Piscitelli98/Progetto-Maturit-/Materiale/Protocolli/Diagrammi Sequenza/Immagini/Protocollo_GetAccessi.png

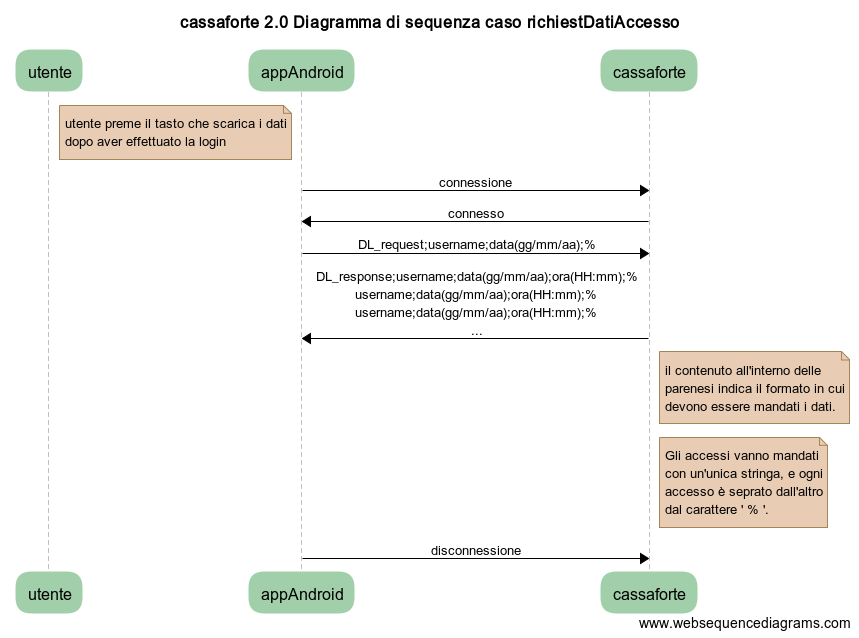
Materiale/Protocolli/Diagrammi Sequenza/Immagini/Protocollo_GetAccessi.png
