Piscitelli98/Progetto-Maturit-/Materiale/Schemi/Circuito completo.png

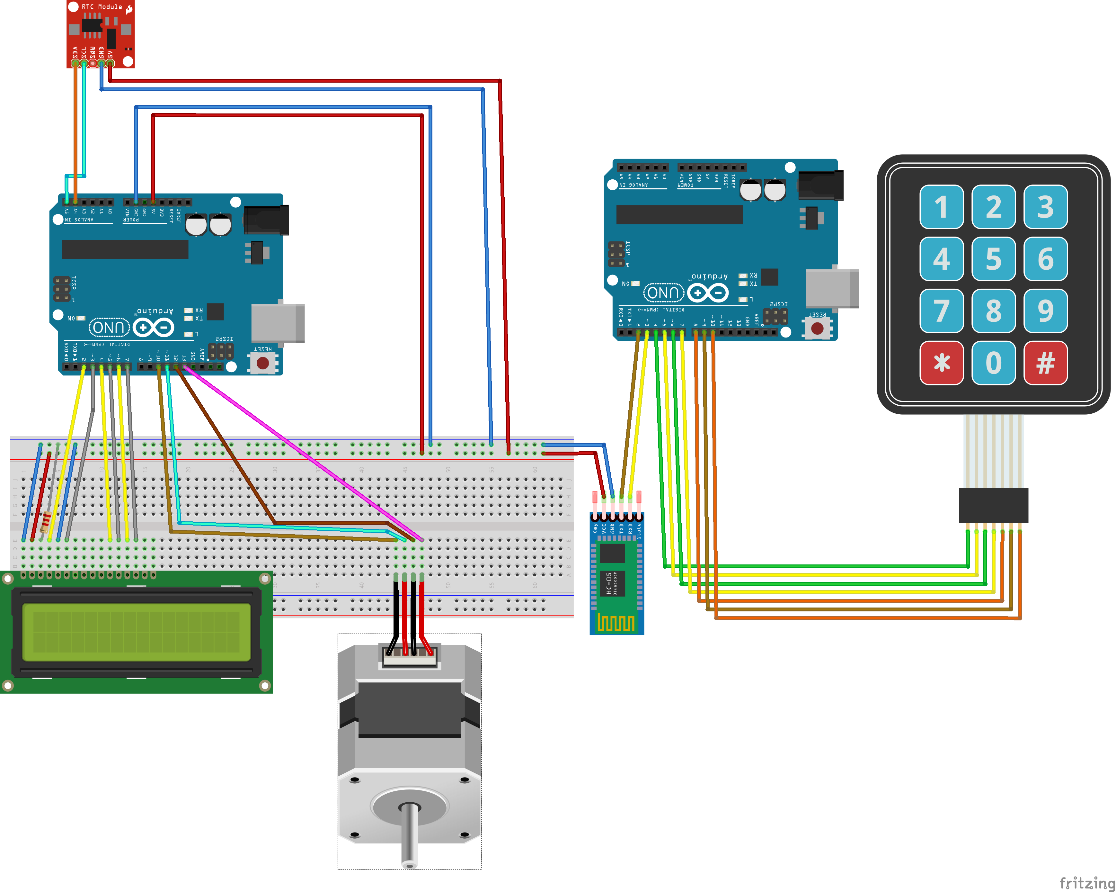
Materiale/Schemi/Circuito completo.png
