Piscitelli98/Progetto-Maturit-/Materiale/Schemi/RTC DS3232.png

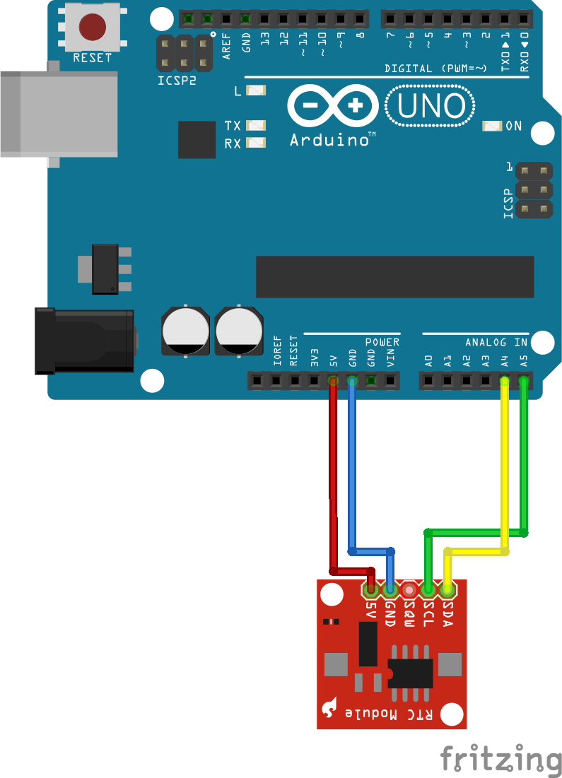
Materiale/Schemi/RTC DS3232.png
