Piscitelli98/Progetto-Maturit-/Materiale/Arduino/arduinoCam.ino

// ArduCAM demo (C)2014 Lee
// web: http://www.ArduCAM.com
// This program is a demo of how to use most of the functions
// of the library with a supported camera modules.
//
// This demo was made for Omnivision OV7670 sensor.
// It will turn the ArduCAM into a real digital camera with capture and playback functions.
// 1. Preview the live video on LCD Screen.
// 2. Capture and buffer the image to FIFO when shutter pressed quickly.
// 3. Store the image to Micro SD/TF card with BMP format.
// 4. Playback the capture photos one by one when shutter buttom hold on for 3 seconds.
// This program requires the ArduCAM V3.1.0 (or above) library and Rev.C ArduCAM shield
// and use Arduino IDE 1.5.2 compiler or above

#include <UTFT_SPI.h>
#include <SD.h>
#include <Wire.h>
#include <ArduCAM.h>
#include <SPI.h>
#include "memorysaver.h"

#if defined(__arm__)
  #include <itoa.h>
#endif

#define SD_CS 9 
#define BMPIMAGEOFFSET 66

// set pin 10 as the slave select for the ArduCAM shield
const int SPI_CS = 10;

const char bmp_header[BMPIMAGEOFFSET] PROGMEM =
{
      0x42, 0x4D, 0x36, 0x58, 0x02, 0x00, 0x00, 0x00, 0x00, 0x00, 0x42, 0x00, 0x00, 0x00, 0x28, 0x00, 
      0x00, 0x00, 0x40, 0x01, 0x00, 0x00, 0xF0, 0x00, 0x00, 0x00, 0x01, 0x00, 0x10, 0x00, 0x03, 0x00, 
      0x00, 0x00, 0x00, 0x58, 0x02, 0x00, 0xC4, 0x0E, 0x00, 0x00, 0xC4, 0x0E, 0x00, 0x00, 0x00, 0x00, 
      0x00, 0x00, 0x00, 0x00, 0x00, 0x00, 0x00, 0xF8, 0x00, 0x00, 0xE0, 0x07, 0x00, 0x00, 0x1F, 0x00,
      0x00, 0x00
};
  


ArduCAM myCAM(OV7670,SPI_CS);
UTFT myGLCD(SPI_CS);

void setup()
{
  uint8_t vid,pid;
  uint8_t temp; 
  
  #if defined (__AVR__)
    Wire.begin(); 
  #endif
  #if defined(__arm__)
    Wire1.begin(); 
  #endif
  Serial.begin(115200);
  Serial.println("ArduCAM Start!"); 

  // set the SPI_CS as an output:
  pinMode(SPI_CS, OUTPUT);

  // initialize SPI:
  SPI.begin(); 
  //Check if the ArduCAM SPI bus is OK
  myCAM.write_reg(ARDUCHIP_TEST1, 0x55);
  temp = myCAM.read_reg(ARDUCHIP_TEST1);
  if(temp != 0x55)
  {
    Serial.println("SPI interface Error!");
    while(1);
  }
  
  //Change MCU mode
  myCAM.set_mode(MCU2LCD_MODE);
  
  //Initialize the LCD Module
  myGLCD.InitLCD();
  
  myCAM.InitCAM();
  
  //Initialize SD Card
  if (!SD.begin(SD_CS)) 
  {
    //while (1);    //If failed, stop here
    Serial.println("SD Card Error");
  }
  else
    Serial.println("SD Card detected!");
}

void loop()
{
  char str[8];
  unsigned long previous_time = 0;
  static int k = 0;
  uint8_t temp;
  myCAM.set_mode(CAM2LCD_MODE);     //Switch to CAM
  
  while(1)
  {

    if(!myCAM.get_bit(ARDUCHIP_TRIG,VSYNC_MASK))        //New Frame is coming
    {
       myCAM.set_mode(MCU2LCD_MODE);      //Switch to MCU
       myGLCD.resetXY();
       myCAM.set_mode(CAM2LCD_MODE);      //Switch to CAM
       while(!myCAM.get_bit(ARDUCHIP_TRIG,VSYNC_MASK));   //Wait for VSYNC is gone
    }
    else if(myCAM.get_bit(ARDUCHIP_TRIG,SHUTTER_MASK))
    {
       previous_time = millis();
       while(myCAM.get_bit(ARDUCHIP_TRIG,SHUTTER_MASK))
       {
         if((millis() - previous_time) > 1500)
         {
           Playback();
         }
       }
       if((millis() - previous_time) < 1500)
       {
         k = k + 1;
         itoa(k, str, 10); 
         strcat(str,".bmp");        //Generate file name
         myCAM.set_mode(MCU2LCD_MODE);      //Switch to MCU, freeze the screen 
         GrabImage(str);
       }
    }
  }
}


void GrabImage(char* str)
{
  File outFile;
  char VH,VL;
  uint8_t temp;
  byte buf[256];
  static int k = 0;
  int i,j = 0;
  
  outFile = SD.open(str,O_WRITE | O_CREAT | O_TRUNC);
  if (! outFile) 
  {
    Serial.println("Open File Error");
    return;
  }
    
  //Switch to FIFO Mode
  myCAM.write_reg(ARDUCHIP_TIM, MODE_MASK);
  //Flush the FIFO 
  myCAM.flush_fifo();    
  //Start capture
  myCAM.start_capture();
  Serial.println("Start Capture"); 

  //Polling the capture done flag
  while(!myCAM.get_bit(ARDUCHIP_TRIG,CAP_DONE_MASK));
  Serial.println("Capture Done!");
  
  k = 0;
  //Write the BMP header
  for( i = 0; i < BMPIMAGEOFFSET; i++)
  {
    char ch = pgm_read_byte(&bmp_header[i]);
    buf[k++] = ch;
  }
  outFile.write(buf,k);
  //Read first dummy byte
  //myCAM.read_fifo();

  k = 0;
  //Read 320x240x2 byte from FIFO
  //Save as RGB565 bmp format
  for(i = 0; i < 240; i++)
    for(j = 0; j < 320; j++)
  {
      VH = myCAM.read_fifo();
      VL = myCAM.read_fifo();
      buf[k++] = VL;
      buf[k++] = VH;
      //Write image data to bufer if not full
      if(k >= 256)
      {
        //Write 256 bytes image data to file from buffer
        outFile.write(buf,256);
        k = 0;
      }
  }
  //Close the file  
  outFile.close(); 
  //Clear the capture done flag 
  myCAM.clear_fifo_flag();
  
  //Switch to LCD Mode
  myCAM.write_reg(ARDUCHIP_TIM, 0);
  return;
}   

void Playback()
{
  File inFile;
  char str[8];
  int k = 0;
  myCAM.set_mode(MCU2LCD_MODE);       //Switch to MCU
  myGLCD.InitLCD(PORTRAIT);
  
  while(1)
  {
      k = k + 1;
      itoa(k, str, 10); 
      strcat(str,".bmp");
      inFile = SD.open(str,FILE_READ);
      if (! inFile) 
        return;
      myGLCD.clrScr();
      //myGLCD.resetXY();
      dispBitmap(inFile);
      inFile.close();
      delay(2000);
  }
}
//Only support RGB565 bmp format
void dispBitmap(File inFile)
{
  char VH,VL;
  int i,j = 0;
  for(i = 0 ;i < BMPIMAGEOFFSET; i++)
    inFile.read();
    for(i = 0; i < 320; i++)
    for(j = 0; j < 240; j++)
    {
      VL = inFile.read();
      //Serial.write(VL);
      VH = inFile.read();
      //Serial.write(VH);
      myGLCD.LCD_Write_DATA(VH,VL);
    }
    myGLCD.clrXY();
}
